abathur8bit/chesslr/src/main/java/img/button-twoPlayerBlack.png

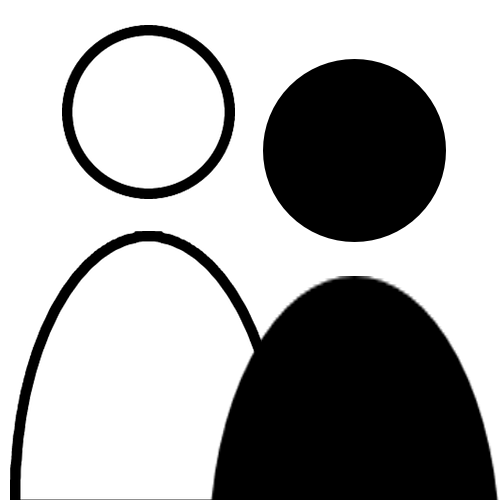
src/main/java/img/button-twoPlayerBlack.png
